charlieyan/snap/data/against_uno_r0x01/F0004TEK.JPG

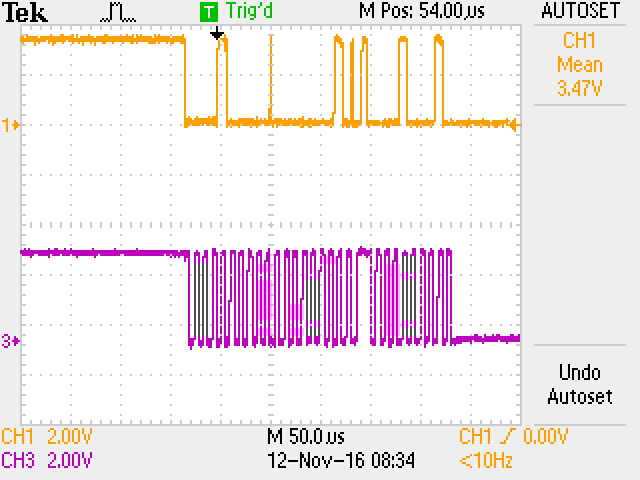
data/against_uno_r0x01/F0004TEK.JPG
