charlieyan/snap/data/ALL0001/F0001TEK.JPG

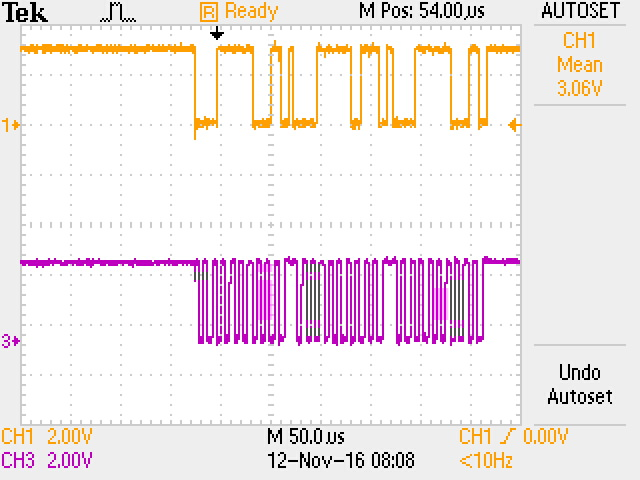
data/ALL0001/F0001TEK.JPG
