charlieyan/snap/data/ALL0003/F0003TEK.JPG

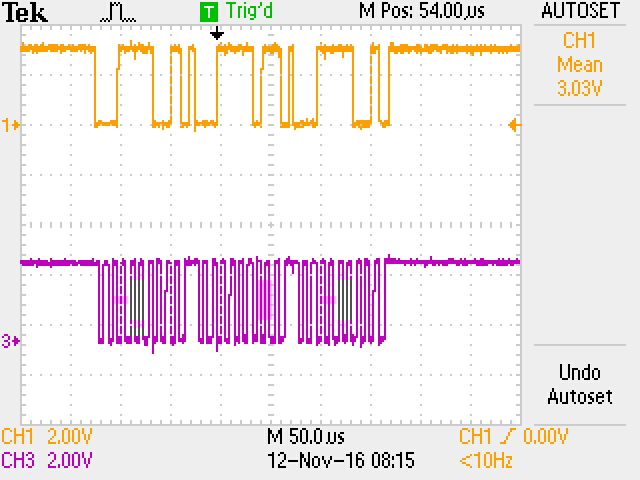
data/ALL0003/F0003TEK.JPG
