charlieyan/snap/data/bigbang/3C_FF_00/F0011TEK.JPG

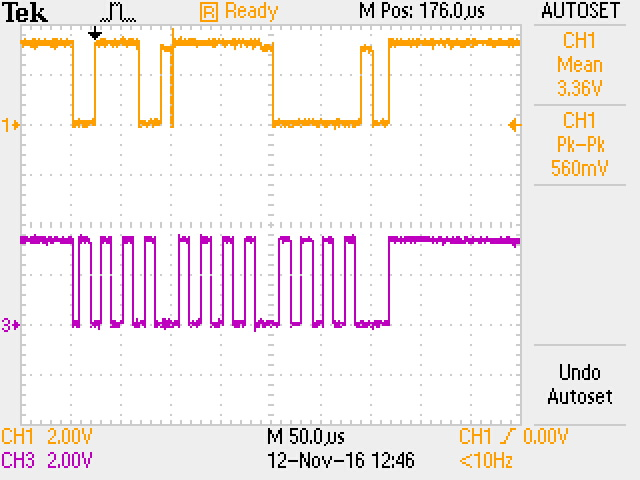
data/bigbang/3C_FF_00/F0011TEK.JPG
