charlieyan/snap/data/bigbang/bit_bang_read/F0001TEK.JPG

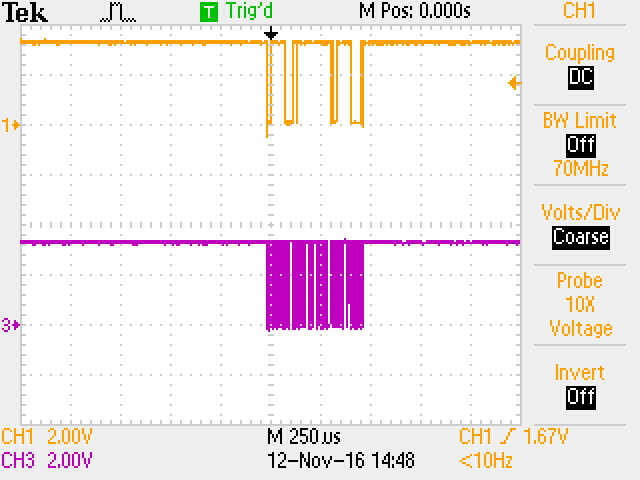
data/bigbang/bit_bang_read/F0001TEK.JPG
