charlieyan/snap/data/bigbang/read_from_30/F0003TEK.JPG

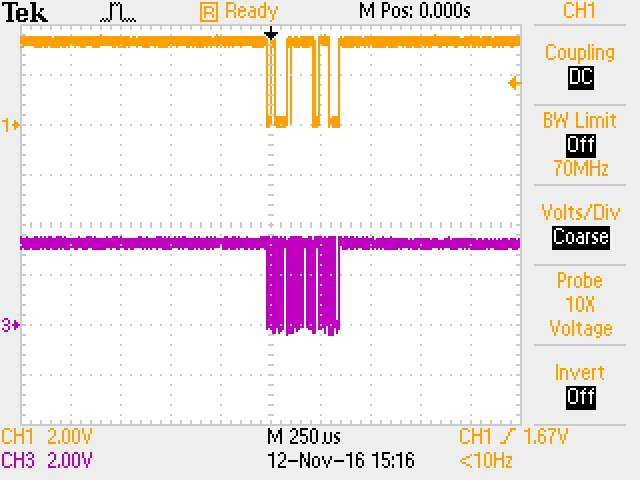
data/bigbang/read_from_30/F0003TEK.JPG
