charlieyan/snap/data/bigbang/read_from_60/F0005TEK.JPG

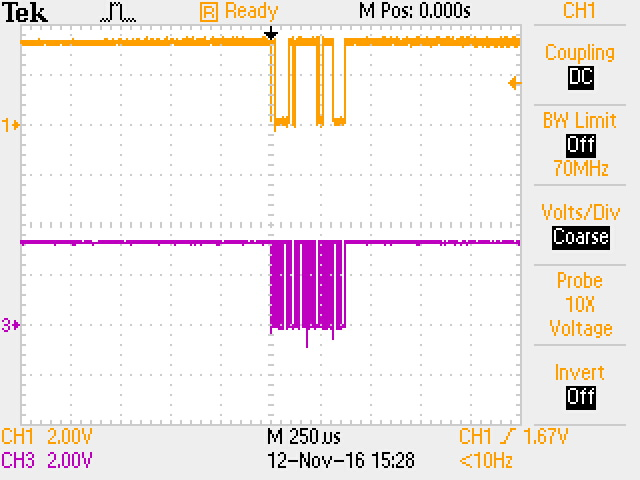
data/bigbang/read_from_60/F0005TEK.JPG
