charlieyan/snap/data/bigbang/read_from_60_better/F0007TEK.JPG

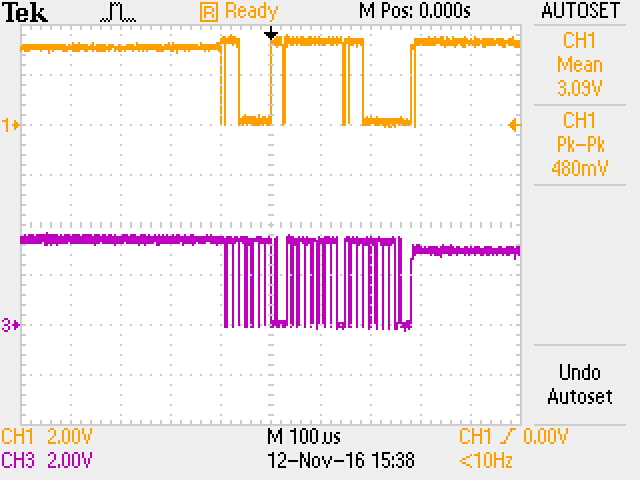
data/bigbang/read_from_60_better/F0007TEK.JPG
