charlieyan/snap/data/bigbang/three_phase_write/F0000TEK.JPG

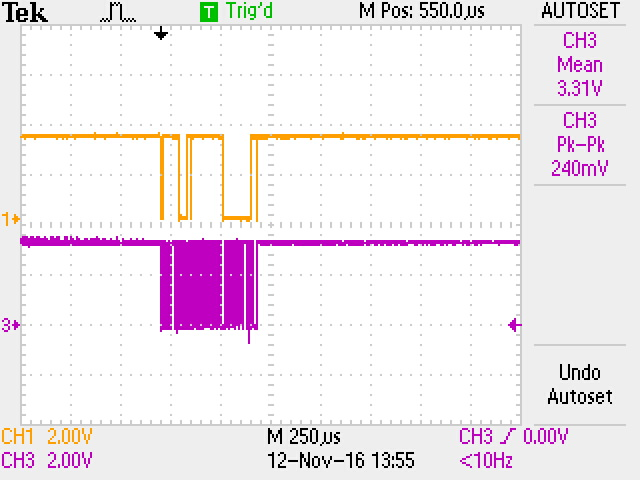
data/bigbang/three_phase_write/F0000TEK.JPG
