charlieyan/snap/data/bigbang/write_to_3c/F0012TEK.JPG

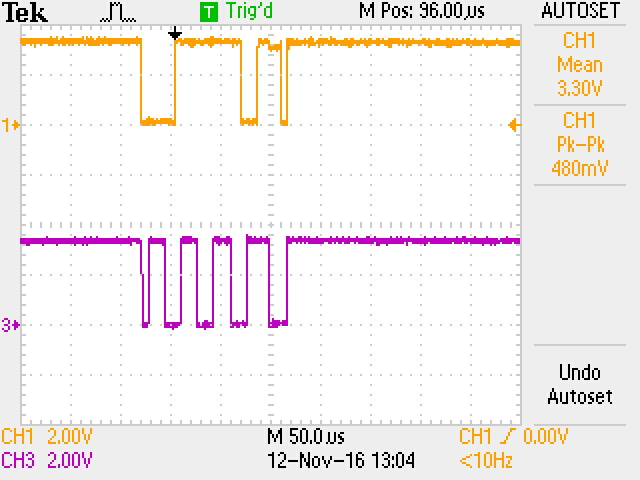
data/bigbang/write_to_3c/F0012TEK.JPG
