charlieyan/snap/data/device_check/F0000TEK.JPG

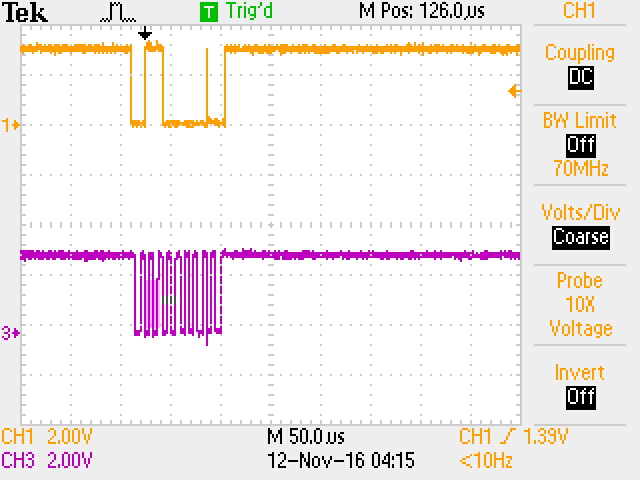
data/device_check/F0000TEK.JPG
