charlieyan/snap/data/latest_r0x04/F0008TEK.JPG

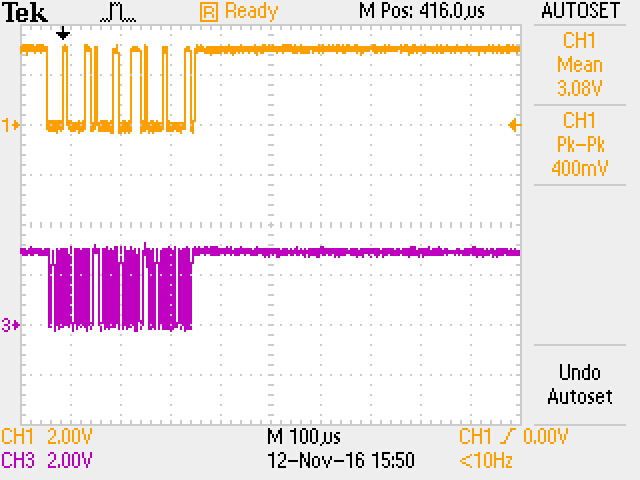
data/latest_r0x04/F0008TEK.JPG
