charlieyan/snap/data/new_r0x08/F0002TEK.JPG

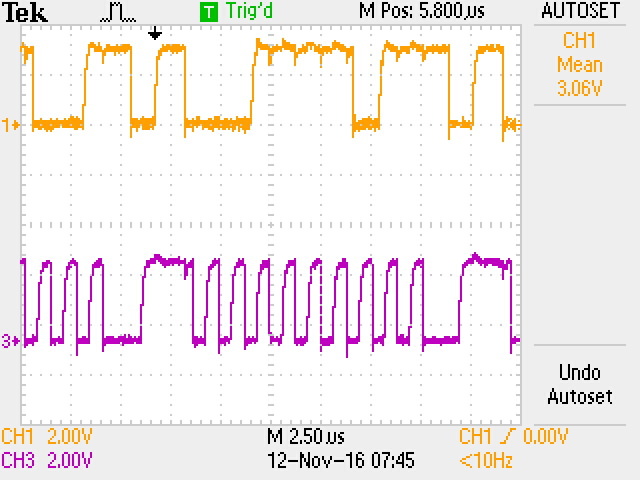
data/new_r0x08/F0002TEK.JPG
