charlieyan/snap/data/new_r0xFF/F0003TEK.JPG

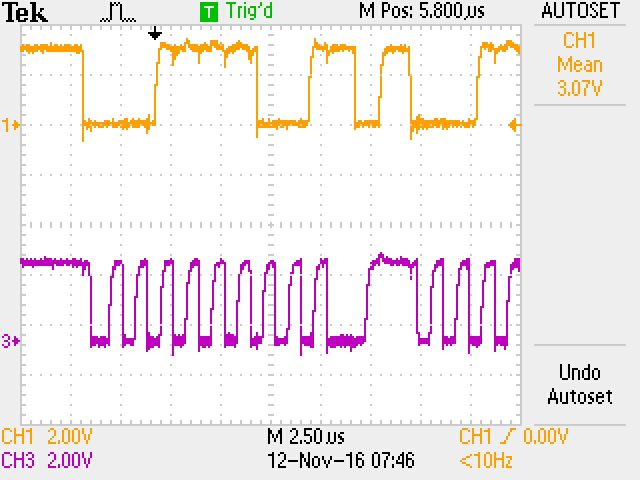
data/new_r0xFF/F0003TEK.JPG
