charlieyan/snap/data/r0x01/F0001TEK.JPG

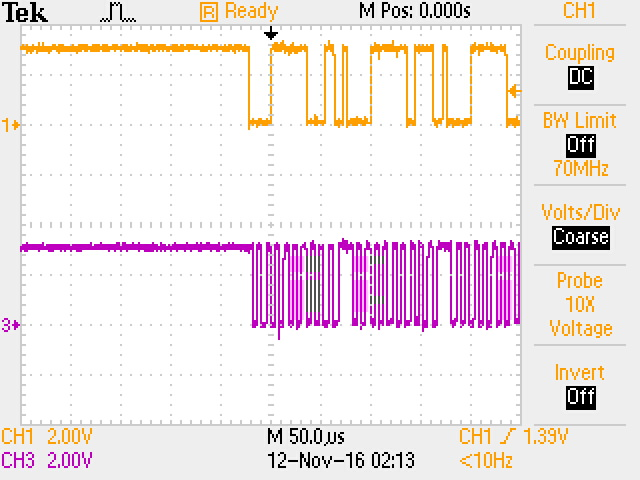
data/r0x01/F0001TEK.JPG
