charlieyan/snap/data/r0x04_actual60/F0010TEK.JPG

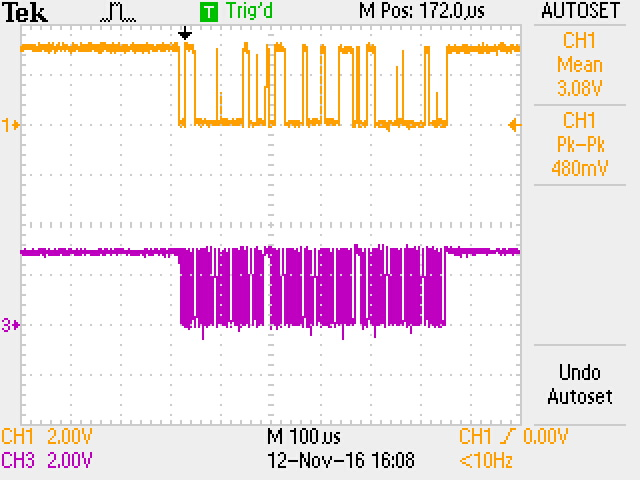
data/r0x04_actual60/F0010TEK.JPG
