charlieyan/snap/data/r0x04_on60/F0009TEK.JPG

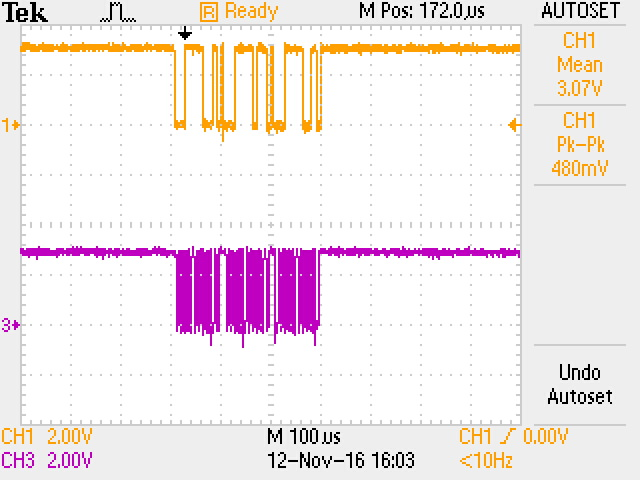
data/r0x04_on60/F0009TEK.JPG
