charlieyan/snap/data/r0x08/F0004TEK.JPG

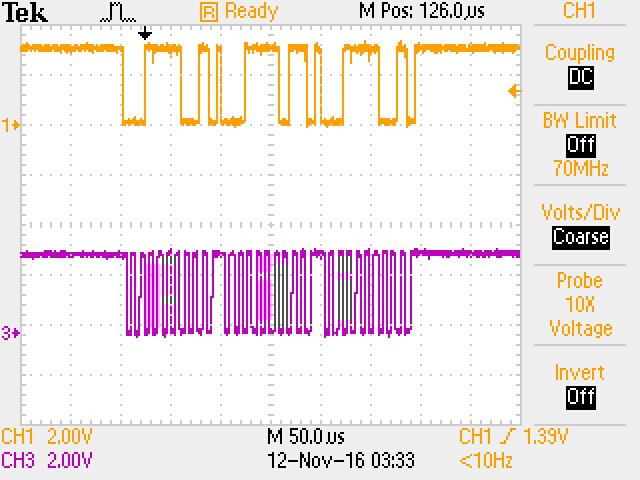
data/r0x08/F0004TEK.JPG
