charlieyan/snap/data/r0xFF.png

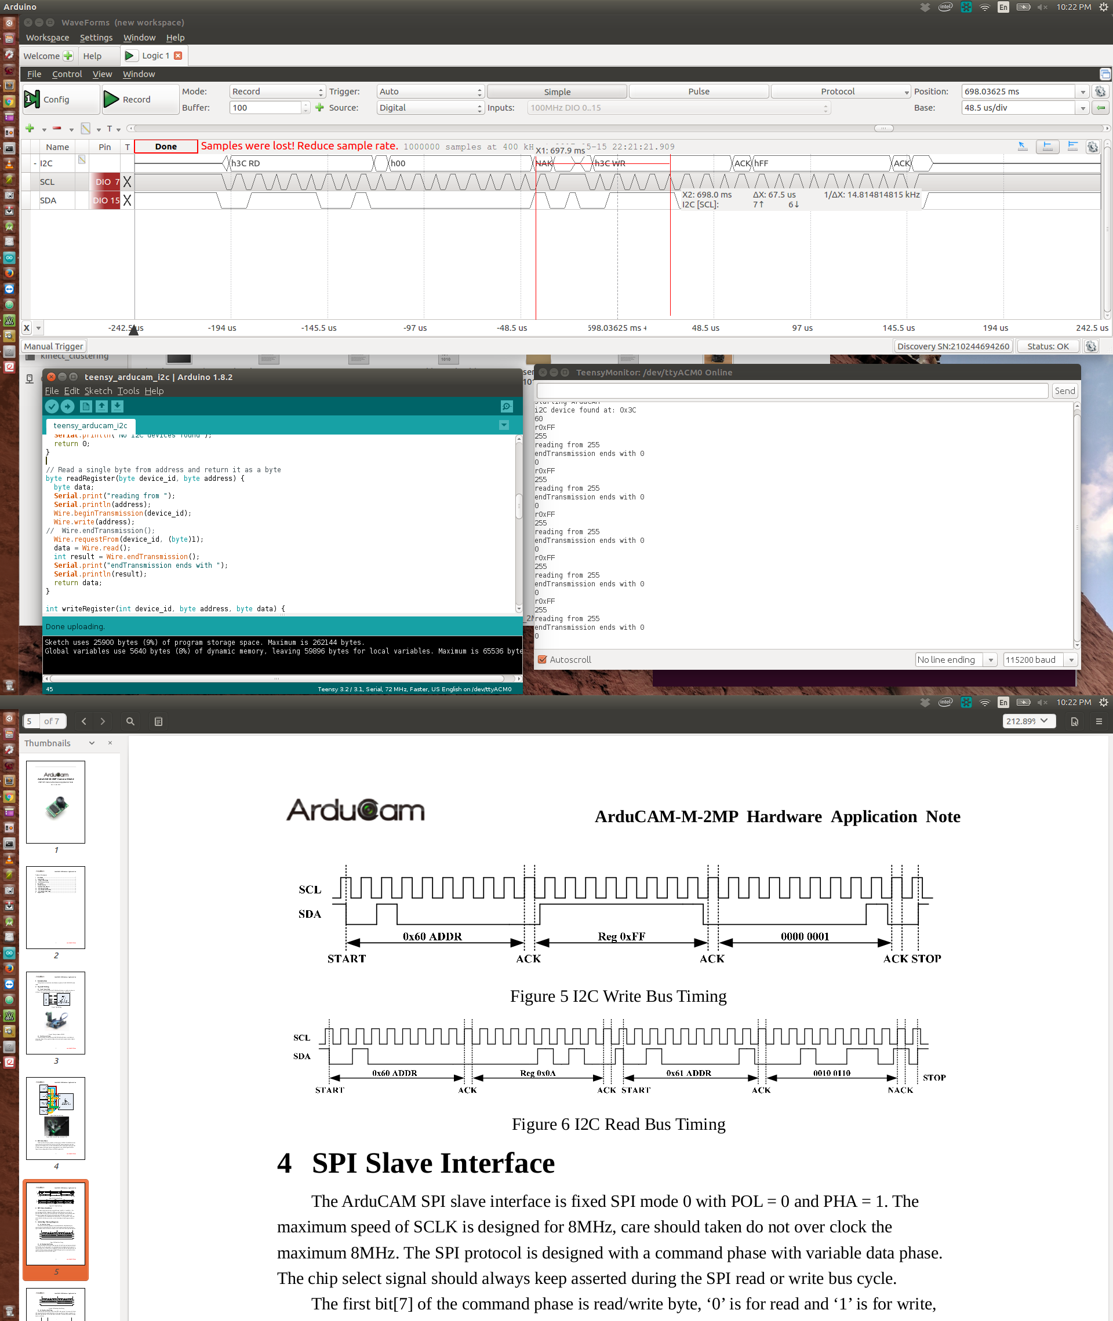
data/r0xFF.png
