charlieyan/snap/data/r0xFF_2/F0000TEK.JPG

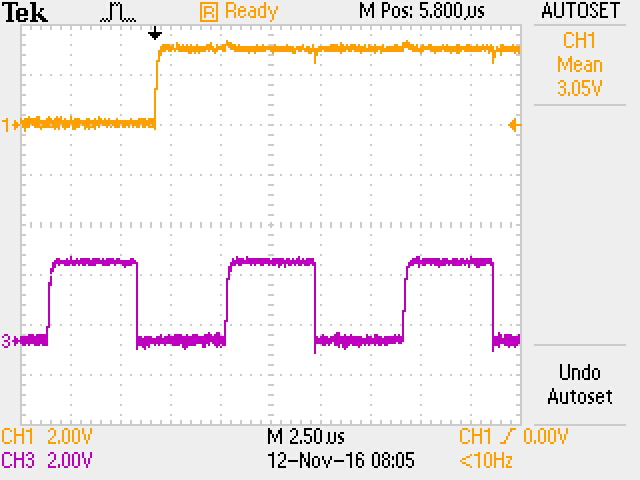
data/r0xFF_2/F0000TEK.JPG
