charlieyan/snap/data/r0xFF_endTransmission.png

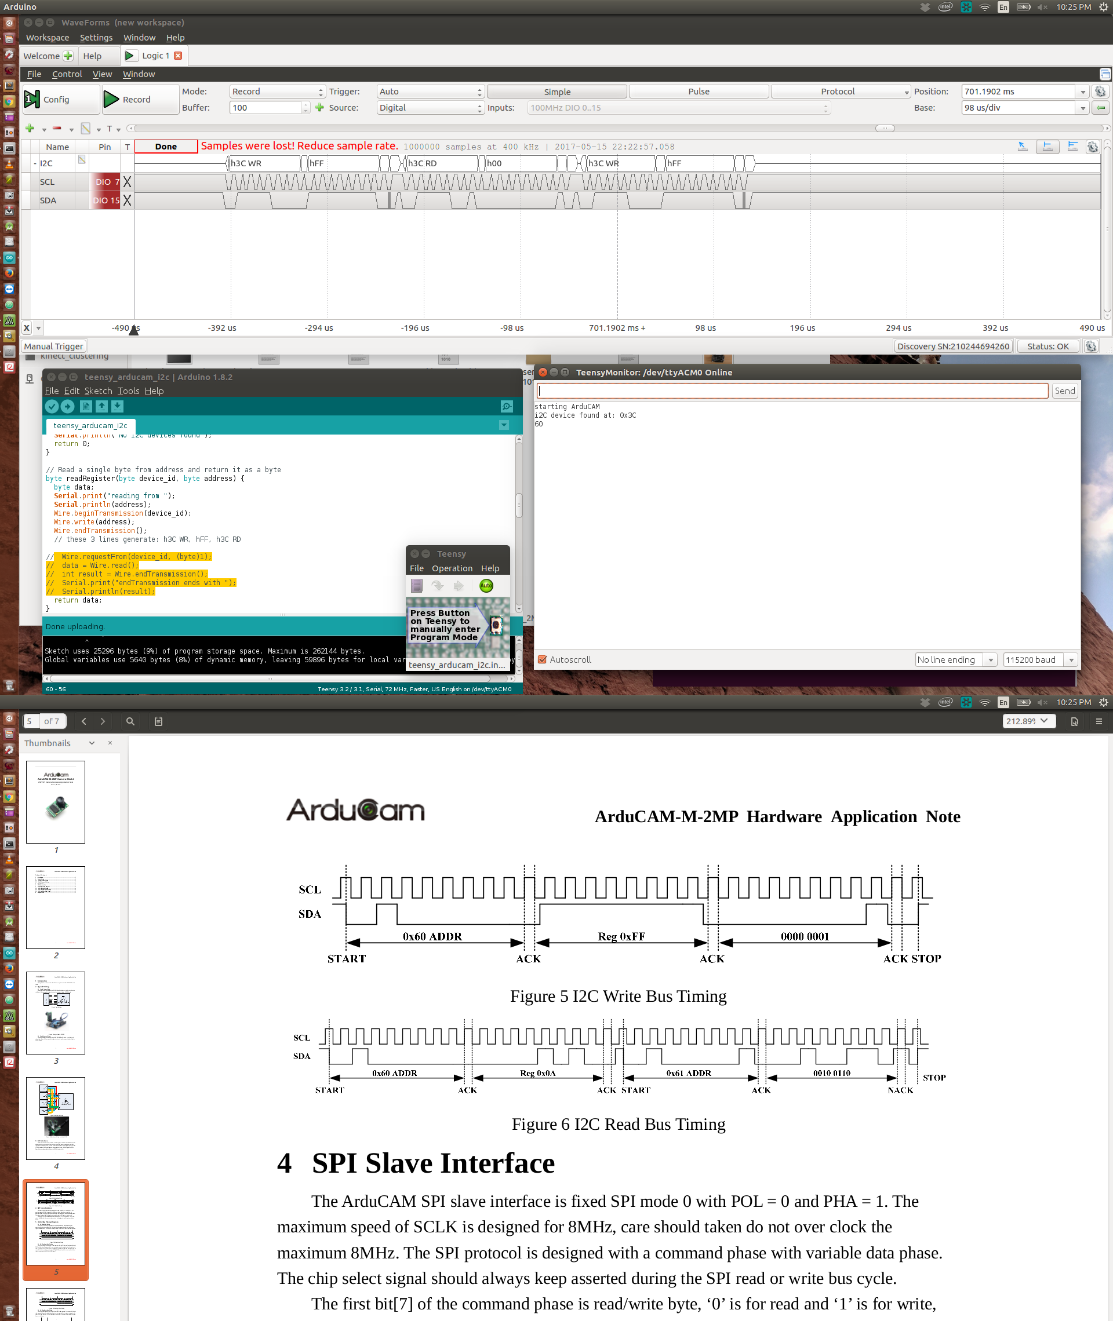
data/r0xFF_endTransmission.png
