charlieyan/snap/data/r0xFF_no_requestfrom.png

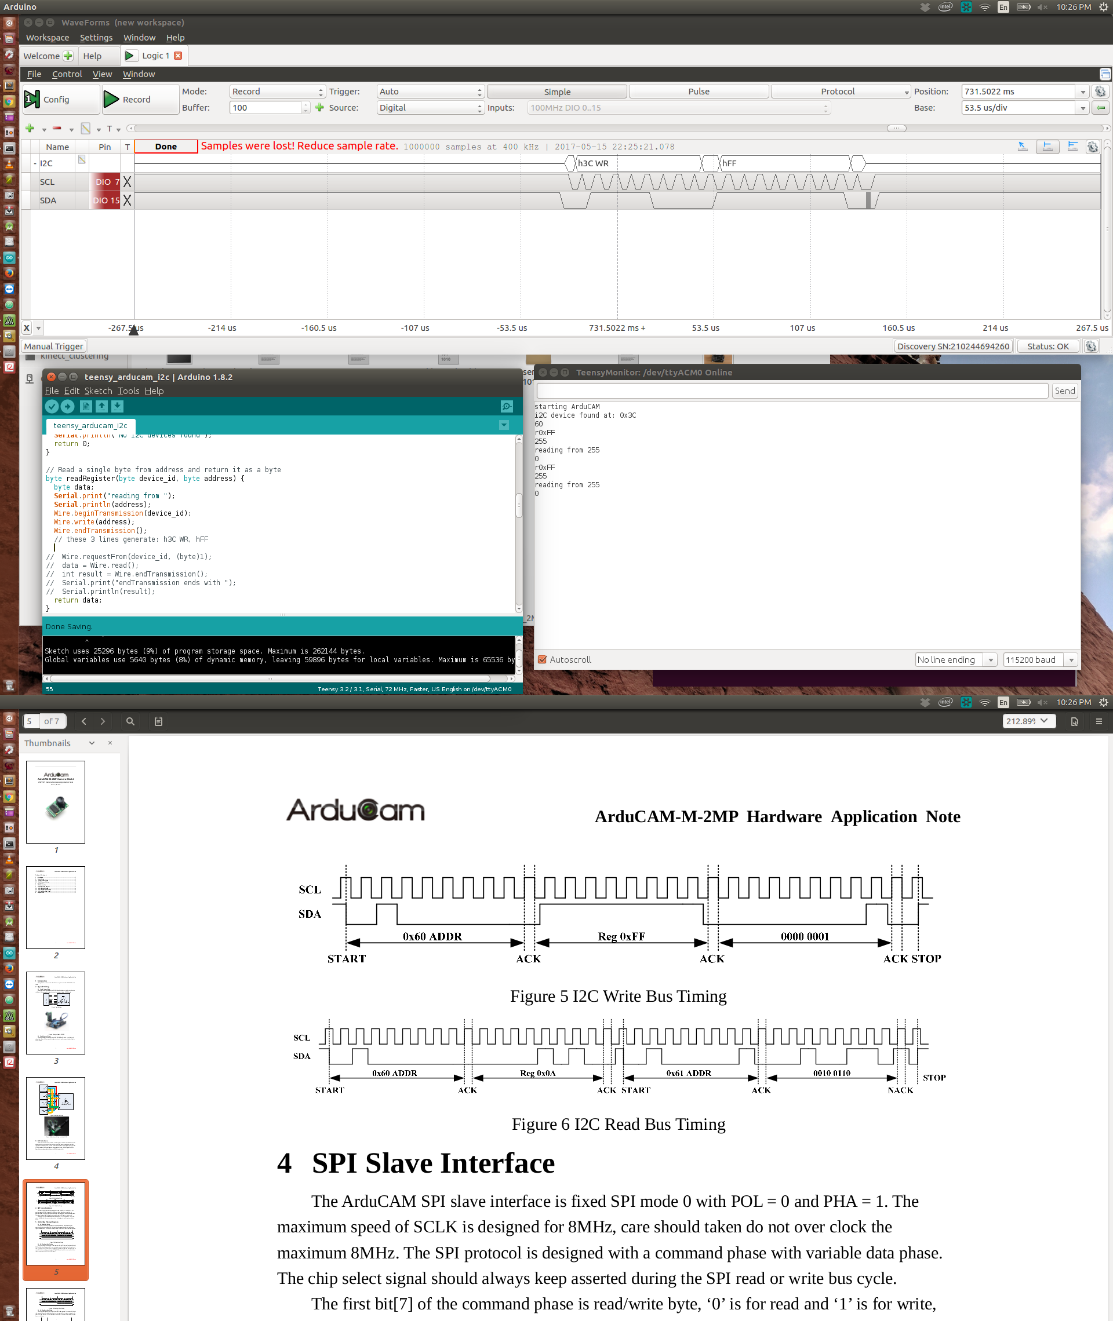
data/r0xFF_no_requestfrom.png
