charlieyan/snap/data/uno_writing_12/r0x00/F0006TEK.JPG

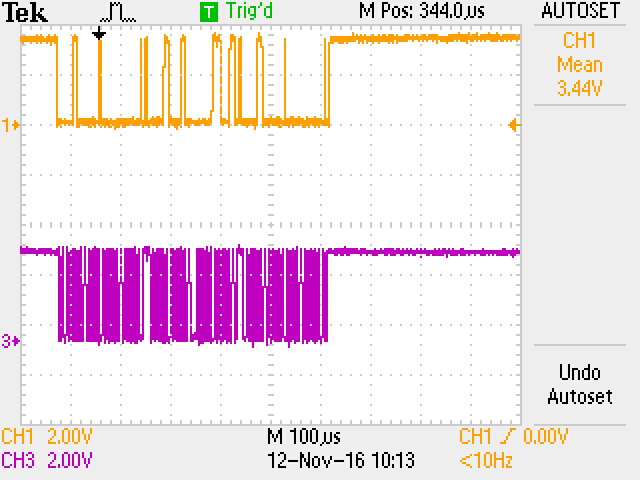
data/uno_writing_12/r0x00/F0006TEK.JPG
