charlieyan/snap/data/uno_writing_12/r0x04/F0007TEK.JPG

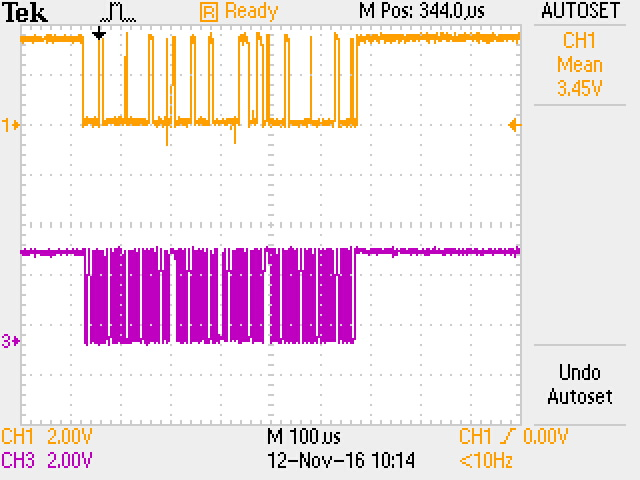
data/uno_writing_12/r0x04/F0007TEK.JPG
