charlieyan/snap/data/uno_writing_12/r0xFF/F0008TEK.JPG

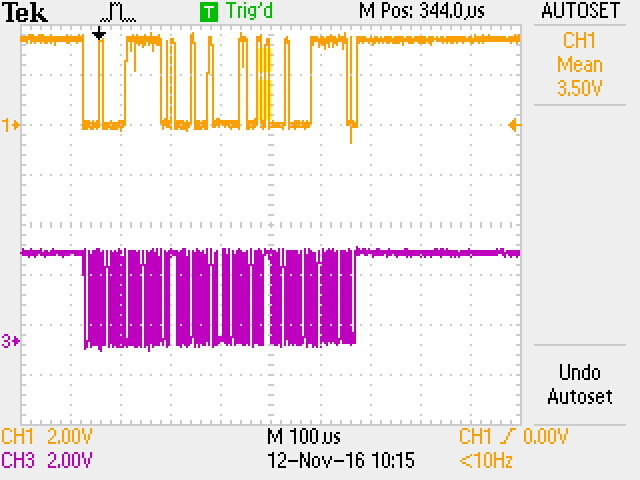
data/uno_writing_12/r0xFF/F0008TEK.JPG
